jyjblrd/Low-Cost-Mocap/sender_esp32/sender_esp32.ino

#include <esp_now.h>
#include <esp_wifi.h>
#include <WiFi.h>

uint8_t broadcastAddresses[][6] = {
  { 0xC0, 0x4E, 0x30, 0x4B, 0x61, 0x3A },
  { 0xC0, 0x4E, 0x30, 0x4B, 0x80, 0x3B },
};

esp_now_peer_info_t peerInfo;

// callback when data is sent
void OnDataSent(const uint8_t *mac_addr, esp_now_send_status_t status) {
  Serial.print("\r\nLast Packet Send Status:\t");
  Serial.println(status == ESP_NOW_SEND_SUCCESS ? "Delivery Success" : "Delivery Fail");
}

void setup() {
  // Init Serial Monitor
  Serial.begin(1000000);

  // Set device as a Wi-Fi Station
  wifi_init_config_t cfg = WIFI_INIT_CONFIG_DEFAULT();
  esp_wifi_init(&cfg);
  esp_wifi_set_mode(WIFI_MODE_STA);
  esp_wifi_set_bandwidth(WIFI_IF_STA, WIFI_BW_HT20);
  esp_wifi_set_storage(WIFI_STORAGE_RAM);
  esp_wifi_set_ps(WIFI_PS_NONE);
  //esp_wifi_set_channel(1, WIFI_SECOND_CHAN_NONE);
  esp_wifi_start();
  
  // Init ESP-NOW
  if (esp_now_init() != ESP_OK) {
    Serial.println("Error initializing ESP-NOW");
    return;
  }
  esp_wifi_config_espnow_rate(WIFI_IF_STA, WIFI_PHY_RATE_24M);
  esp_wifi_start();

  // Init ESP-NOW
  if (esp_now_init() != ESP_OK) {
    Serial.println("Error initializing ESP-NOW");
    return;
  }

  // Once ESPNow is successfully Init, we will register for Send CB to
  // get the status of Trasnmitted packet
  esp_now_register_send_cb(OnDataSent);

  // Register peer
  memcpy(peerInfo.peer_addr, broadcastAddresses[0], 6);
  peerInfo.channel = 0;
  peerInfo.encrypt = false;
  // Add peer
  if (esp_now_add_peer(&peerInfo) != ESP_OK) {
    Serial.println("Failed to add peer");
    return;
  }
  
  memcpy(peerInfo.peer_addr, broadcastAddresses[1], 6);
  peerInfo.channel = 0;
  peerInfo.encrypt = false;
  // Add peer
  if (esp_now_add_peer(&peerInfo) != ESP_OK) {
    Serial.println("Failed to add peer");
    return;
  }
}

char buffer[1024];
void loop() {
  int availableBytes = Serial.available();
  if (availableBytes) {
    int droneIndex = Serial.read() - '0';
    Serial.readBytes(buffer, availableBytes-1);
    buffer[availableBytes-1] = '\0';
    Serial.printf("\n drone index %d: ", droneIndex);
    Serial.print(buffer);

    esp_err_t result = esp_now_send(broadcastAddresses[droneIndex], (uint8_t *)&buffer, strlen(buffer) + 1);
    if (result) {
      Serial.println(esp_err_to_name(result));
    }
  }
  else {
    yield();
  }
}
